wcpthethird/mini-speaker/Reference/NucleoF303UART.png

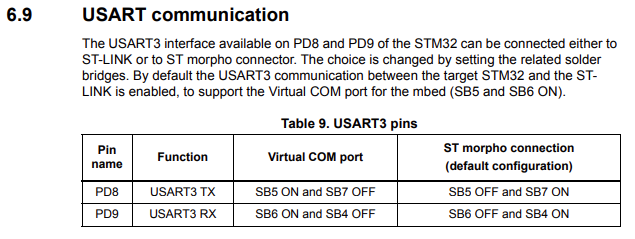
Reference/NucleoF303UART.png
