wcpthethird/mini-speaker/Reference/ADCConfigCube.png

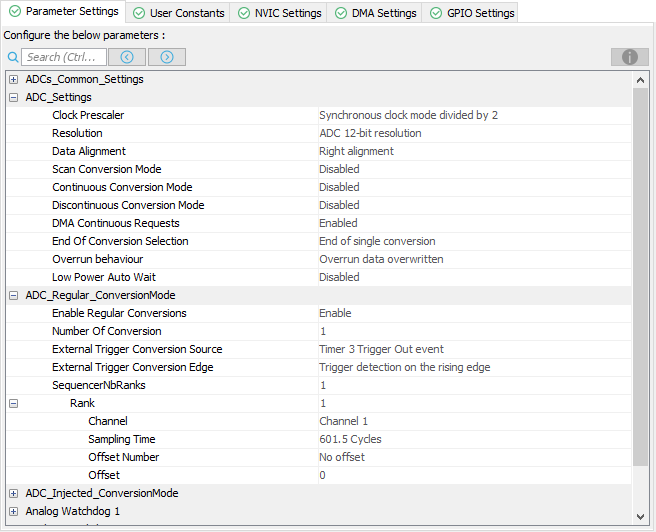
Reference/ADCConfigCube.png
