wcpthethird/mini-speaker/Reference/ADCDataRegister.png

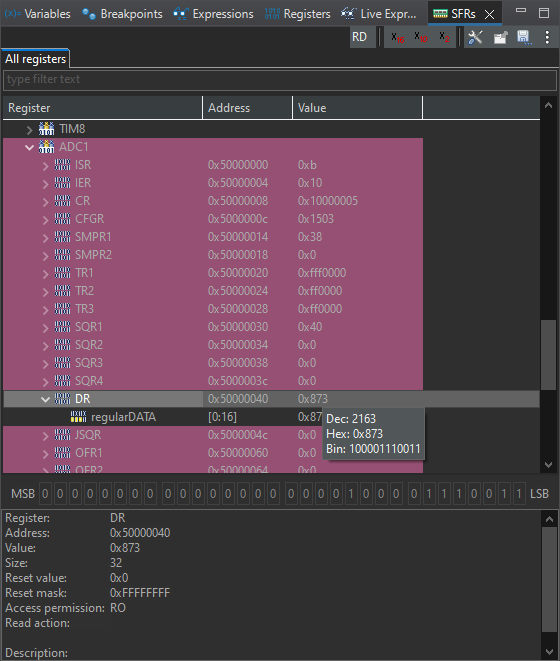
Reference/ADCDataRegister.png
