wcpthethird/mini-speaker/Reference/ADCDataRegisterRM.png

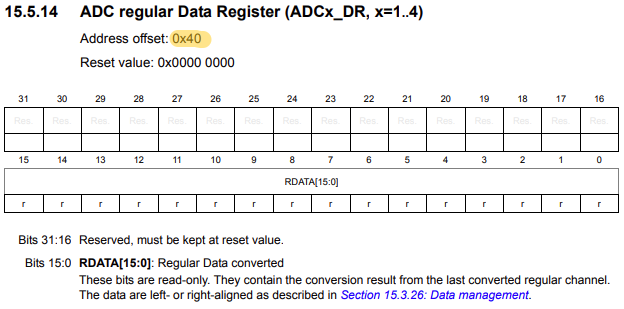
Reference/ADCDataRegisterRM.png
