wcpthethird/mini-speaker/Reference/ADCDMAConfigCube.png

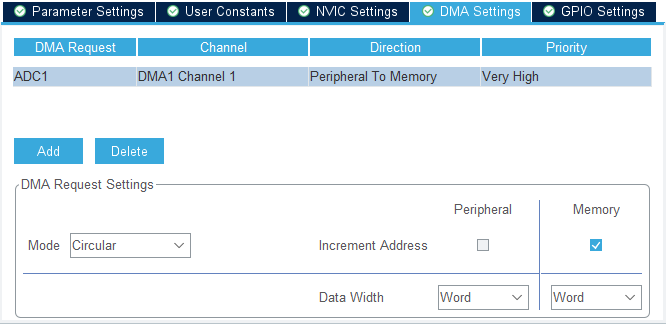
Reference/ADCDMAConfigCube.png
