wcpthethird/mini-speaker/Reference/ADCTimingRM.png

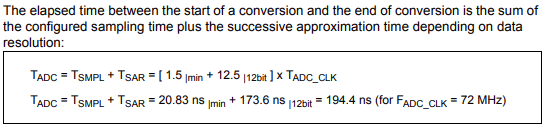
Reference/ADCTimingRM.png
