wcpthethird/mini-speaker/Reference/BPFilter2a.png

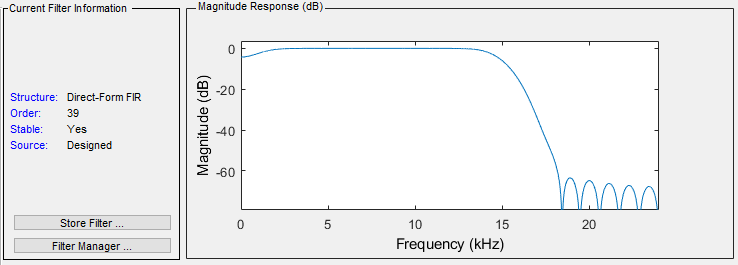
Reference/BPFilter2a.png
