wcpthethird/mini-speaker/Reference/BPFilter2b.png

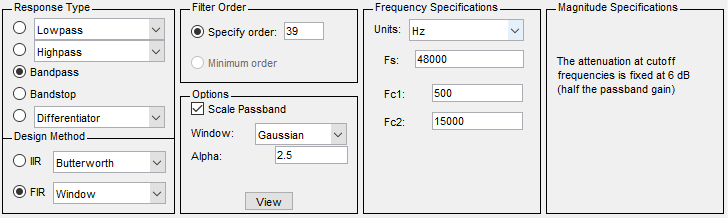
Reference/BPFilter2b.png
