wcpthethird/mini-speaker/Reference/BPFilter.png

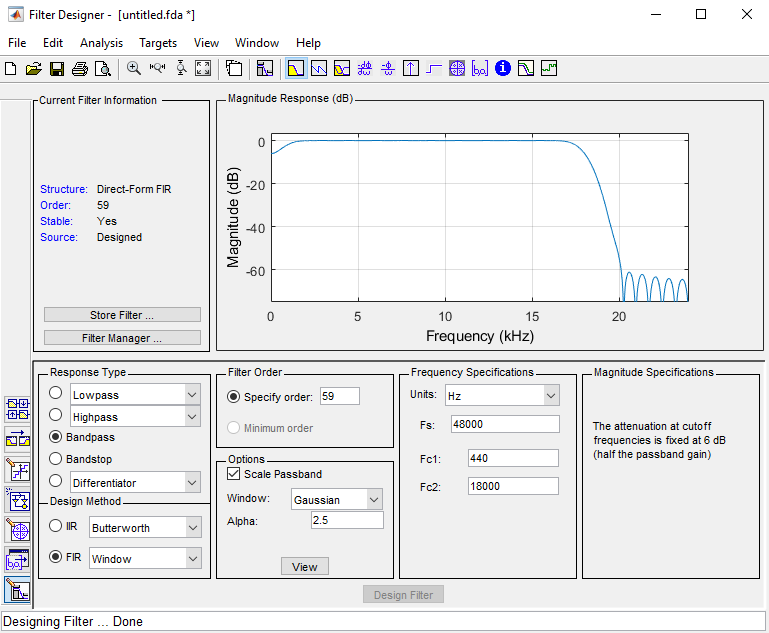
Reference/BPFilter.png
