wcpthethird/mini-speaker/Reference/ClkConfigCube.png

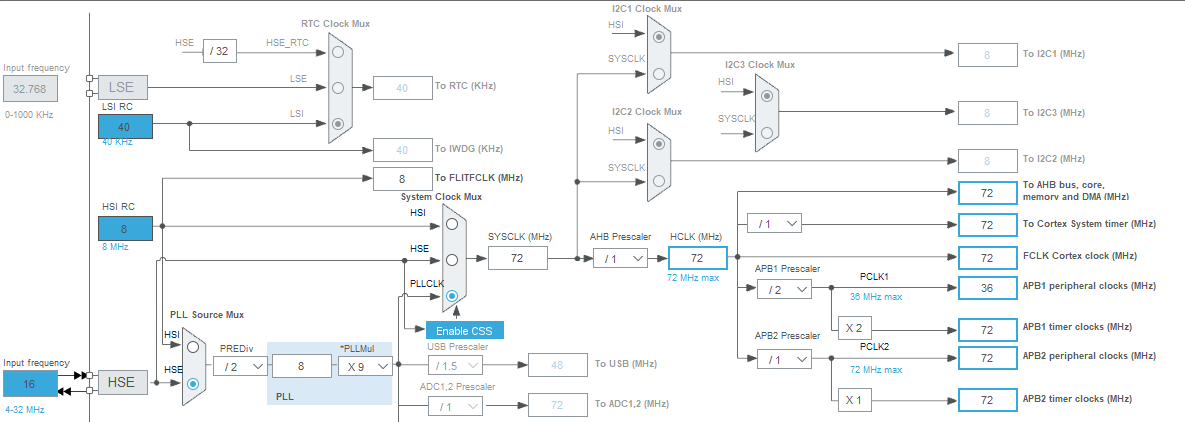
Reference/ClkConfigCube.png
