wcpthethird/mini-speaker/Reference/CMSISFIR.png

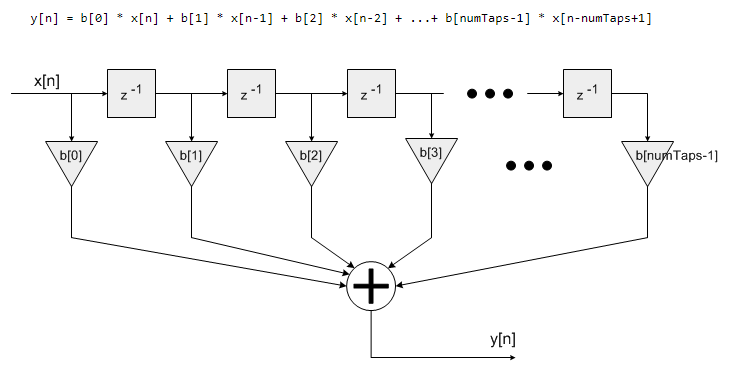
Reference/CMSISFIR.png
