wcpthethird/mini-speaker/Reference/ConvDiagram.png

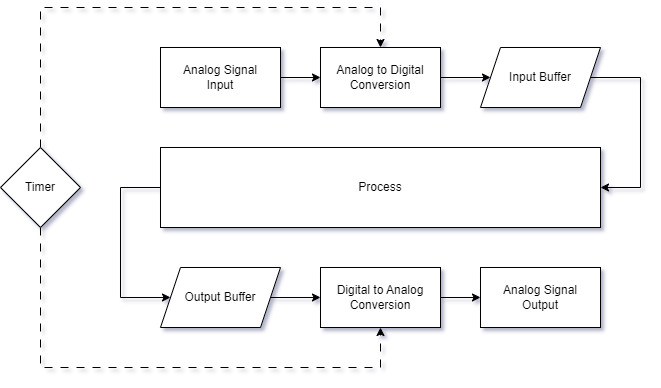
Reference/ConvDiagram.png
