wcpthethird/mini-speaker/Reference/CubeMXDSPSymbol.png

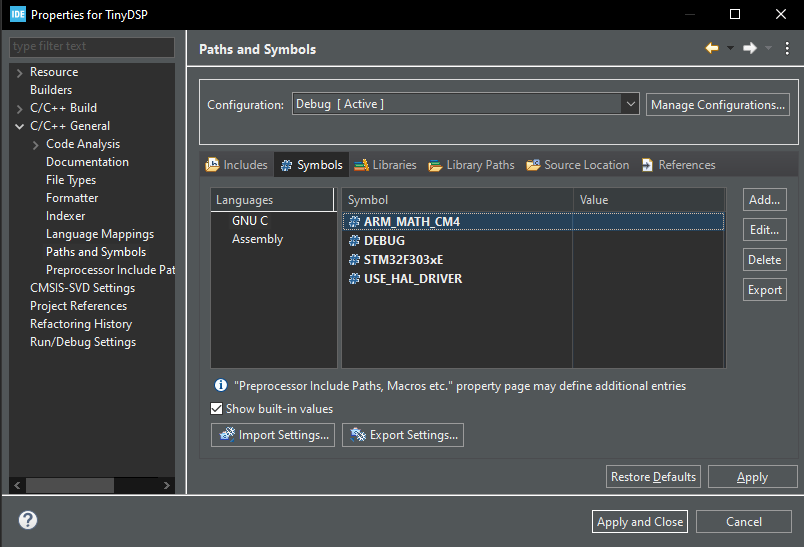
Reference/CubeMXDSPSymbol.png
