wcpthethird/mini-speaker/Reference/DACDataRegister.png

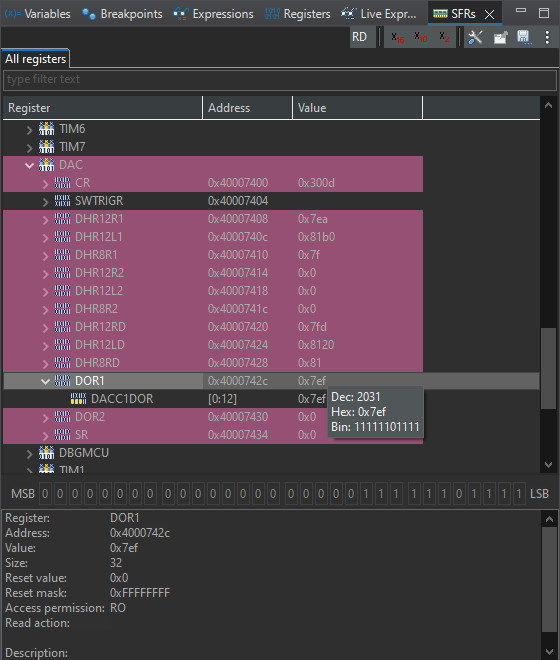
Reference/DACDataRegister.png
