wcpthethird/mini-speaker/Reference/DACDataRegisterRM.png

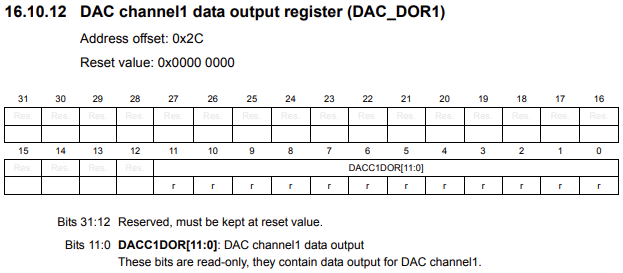
Reference/DACDataRegisterRM.png
