wcpthethird/mini-speaker/Reference/DACDMAConfigCube.png

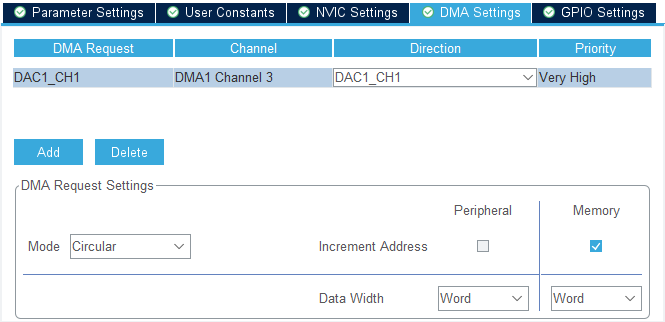
Reference/DACDMAConfigCube.png
