wcpthethird/mini-speaker/Reference/DataPostBias.png

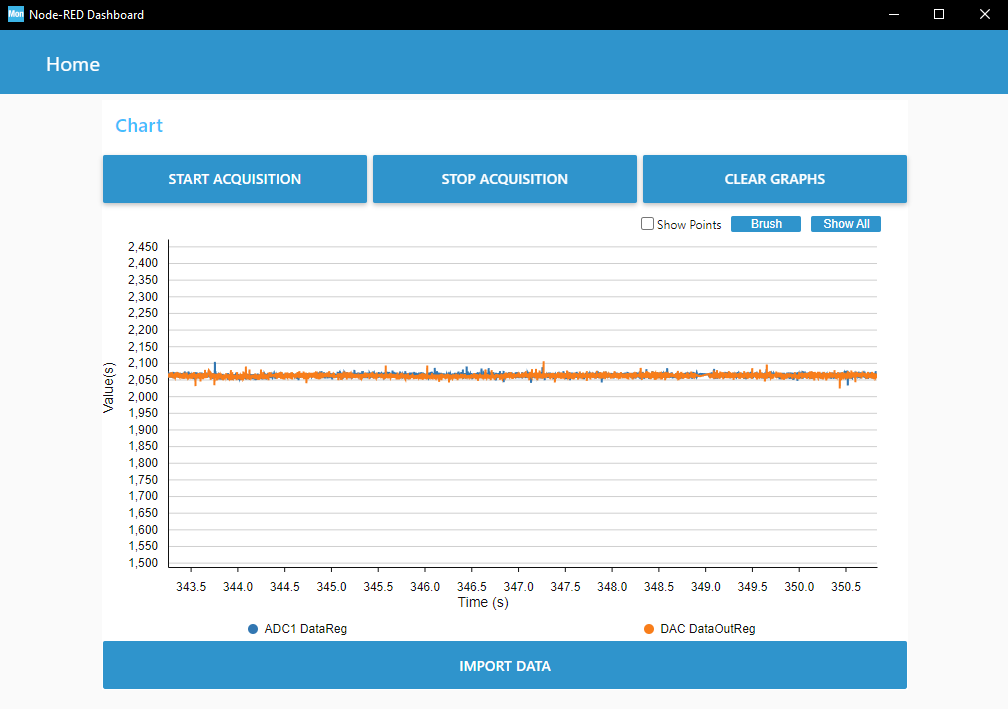
Reference/DataPostBias.png
