wcpthethird/mini-speaker/Reference/DataPreBias.png

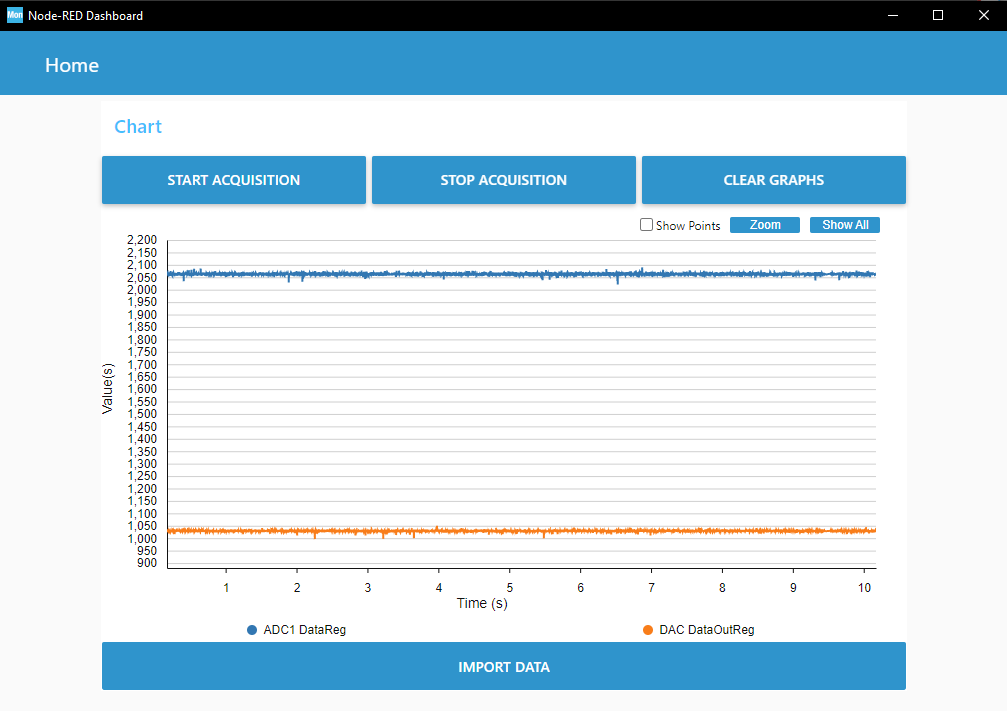
Reference/DataPreBias.png
