wcpthethird/mini-speaker/Reference/LPFilter.png

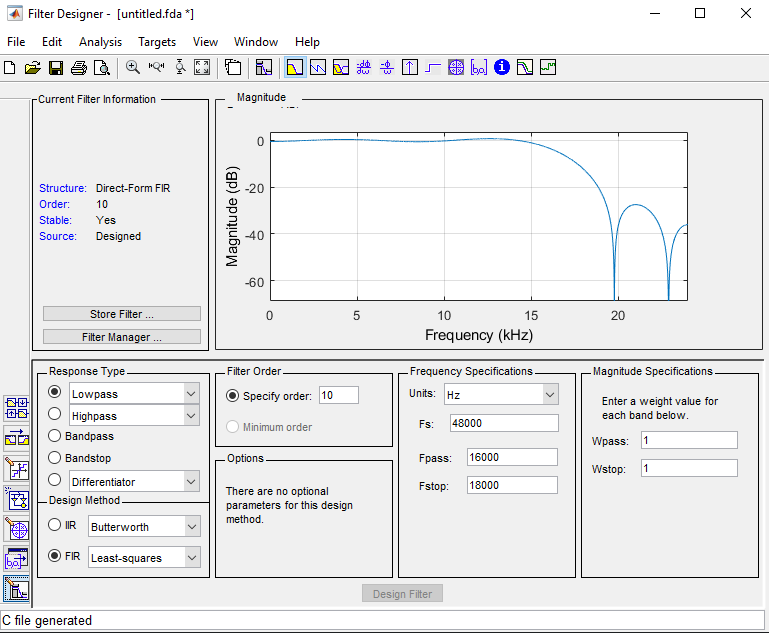
Reference/LPFilter.png
