wcpthethird/mini-speaker/Reference/OpAmpConfigCube.png

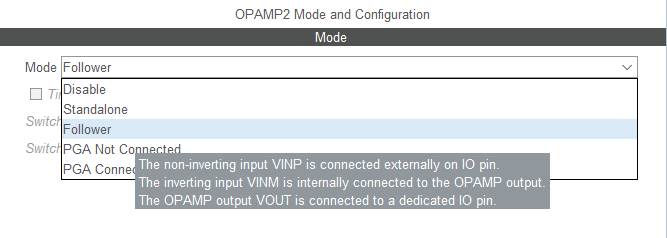
Reference/OpAmpConfigCube.png
