wcpthethird/mini-speaker/Reference/PostFilterSimulink.png

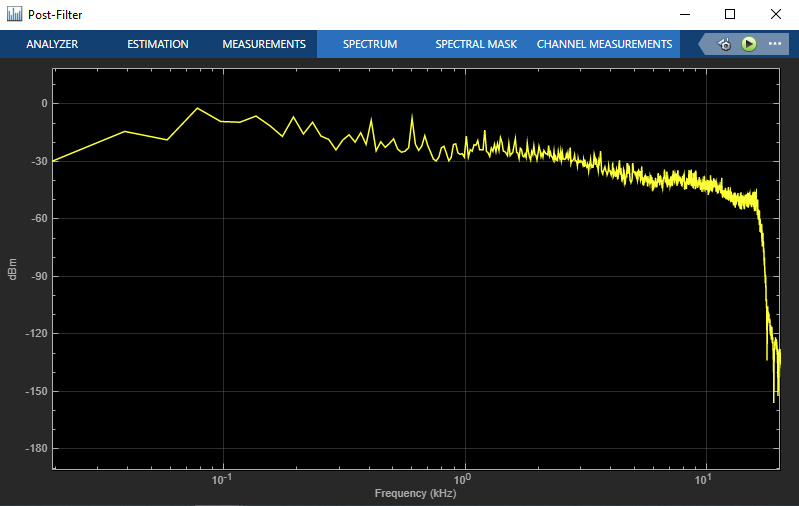
Reference/PostFilterSimulink.png
