wcpthethird/mini-speaker/Reference/Pre-_Post-FilterSimulink.png

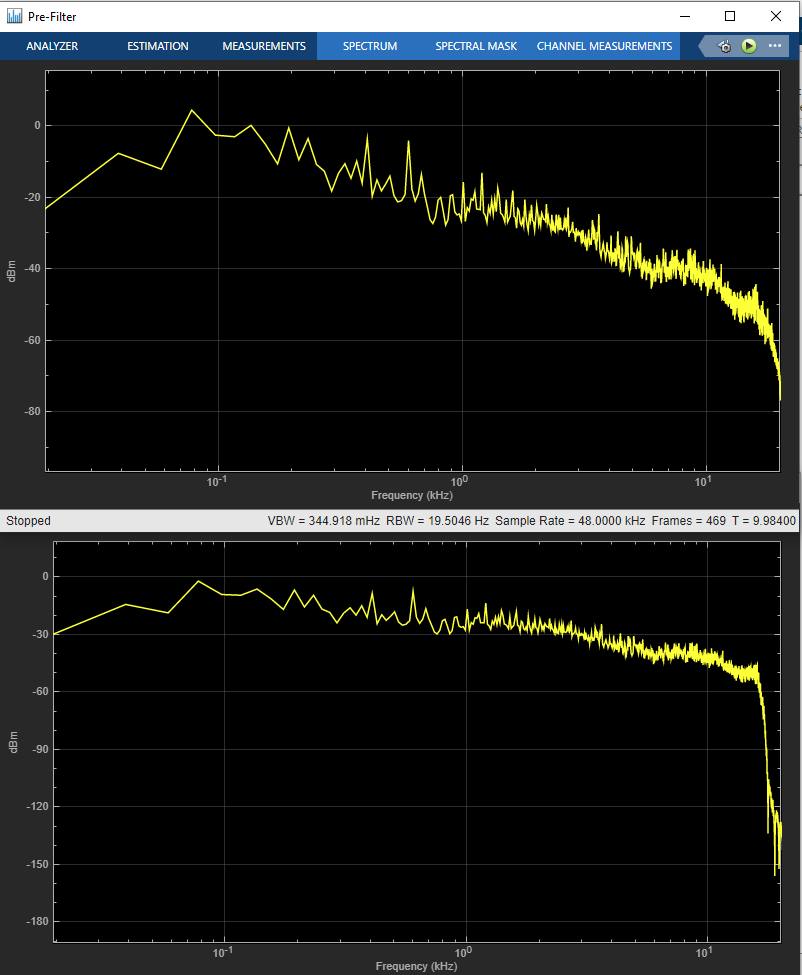
Reference/Pre-_Post-FilterSimulink.png
