wcpthethird/mini-speaker/Reference/PreFilterSimulink.png

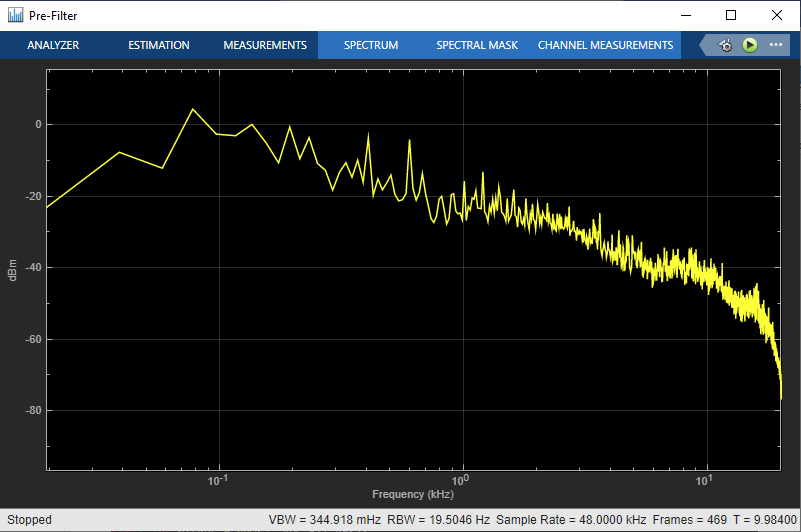
Reference/PreFilterSimulink.png
