wcpthethird/mini-speaker/Reference/Assembly.png

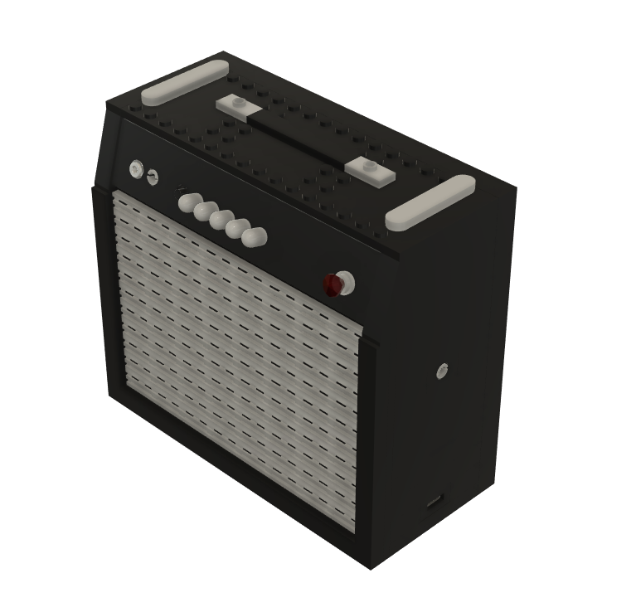
Reference/Assembly.png
