wcpthethird/mini-speaker/Reference/Assembly_EXPLD.png

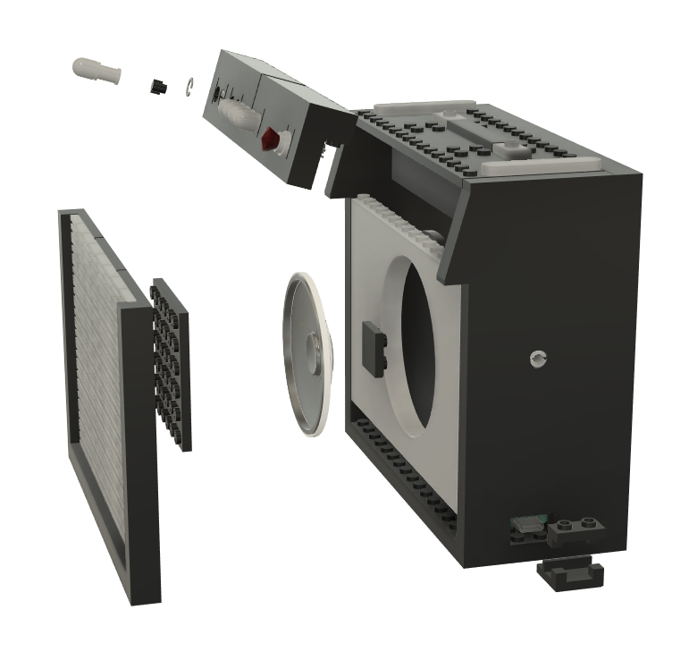
Reference/Assembly_EXPLD.png
